edwindertien/picotonewheel/docs/07_pio_allocation.png

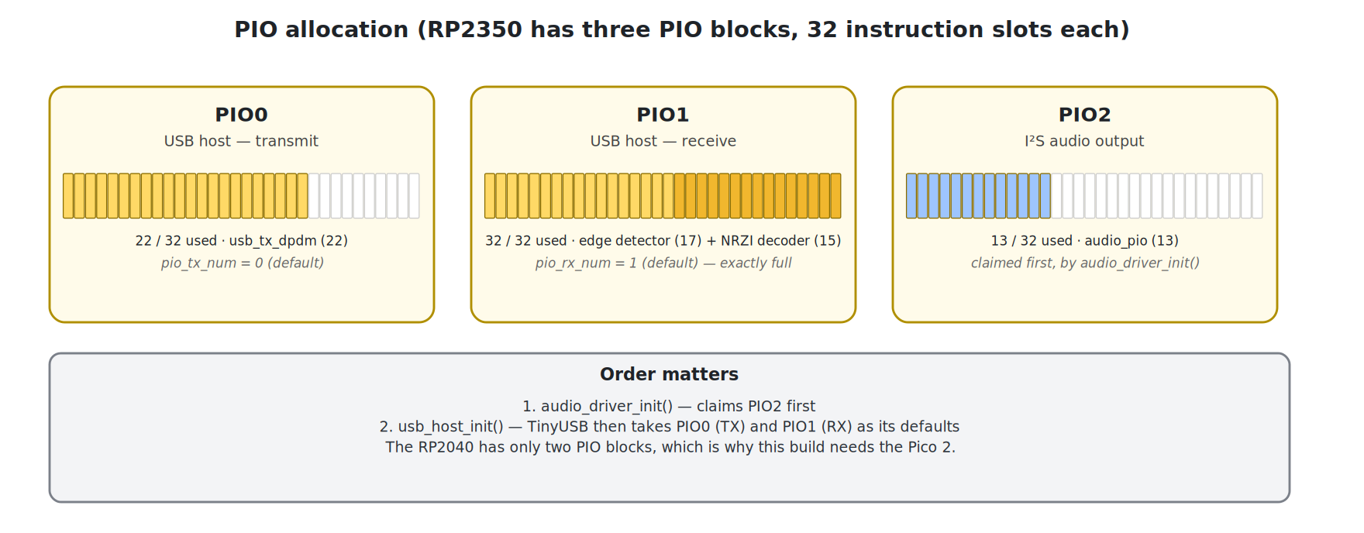
docs/07_pio_allocation.png
