edwindertien/picotonewheel/docs/11_lcd_layout.png

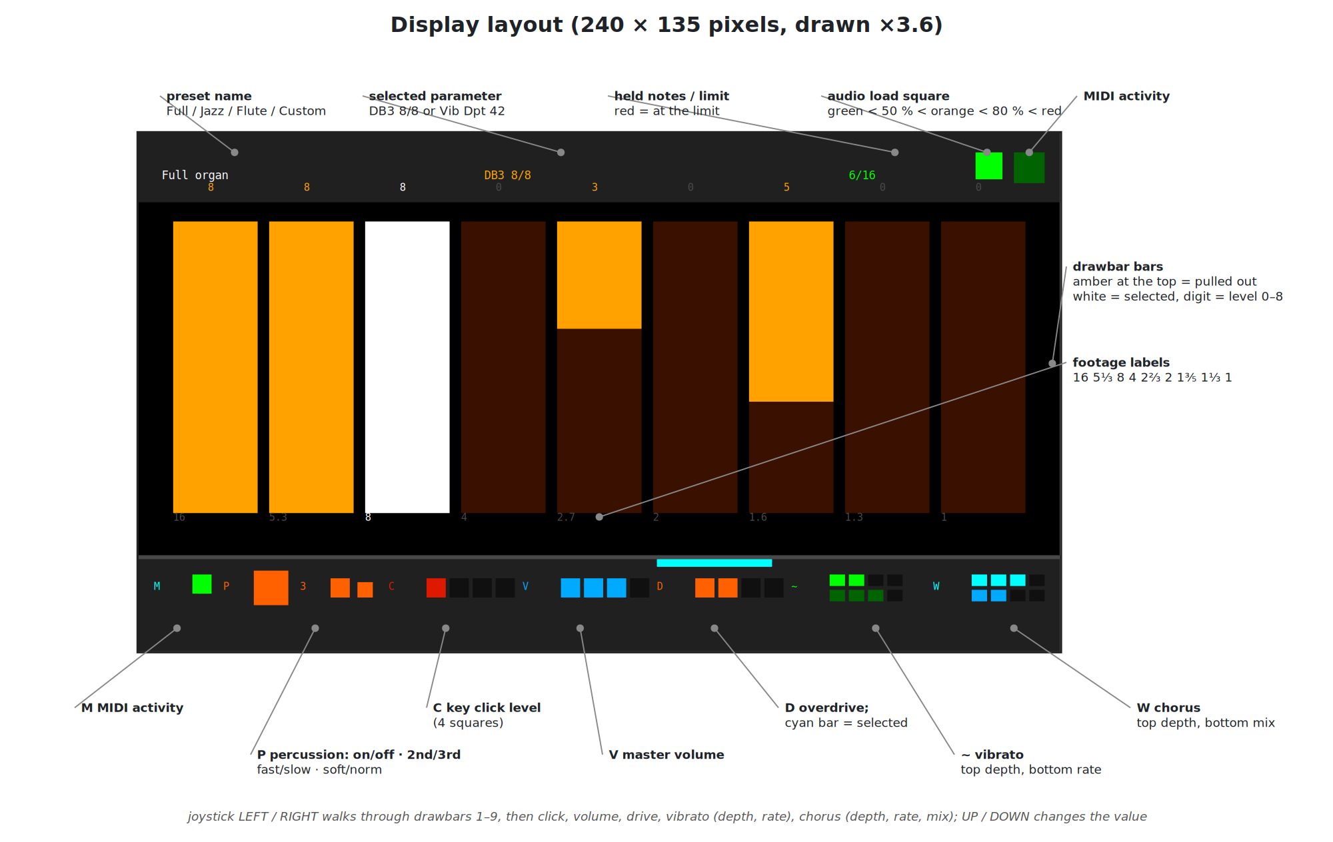
docs/11_lcd_layout.png
