edwindertien/picotonewheel/docs/tonewheel_organ_system.png

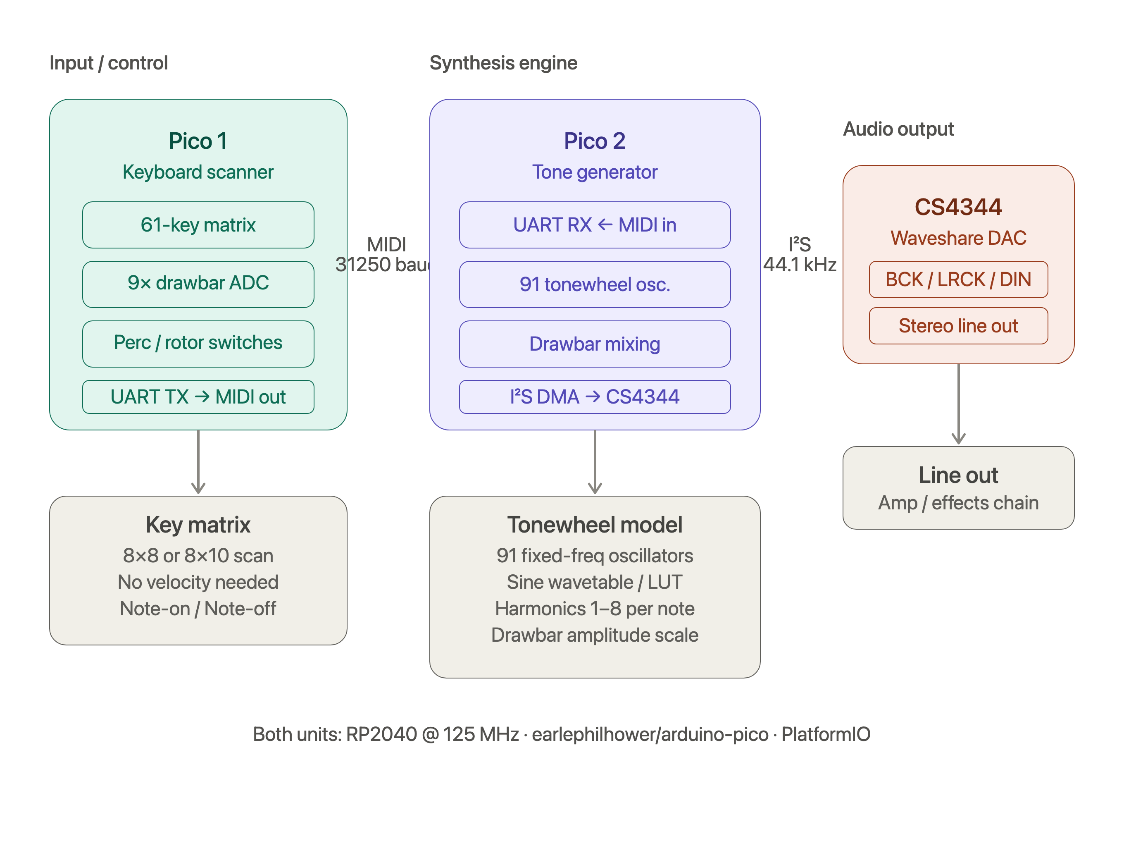
docs/tonewheel_organ_system.png
