edwindertien/picotonewheel/resources/Pico-Audio - Waveshare Wiki_files/300px-Pico-Audio-1.jpg

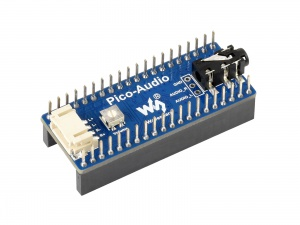
resources/Pico-Audio - Waveshare Wiki_files/300px-Pico-Audio-1.jpg
