edwindertien/picotonewheel/resources/Pico-Audio - Waveshare Wiki_files/300px-Pico-vscode-3.png

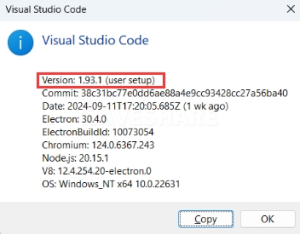
resources/Pico-Audio - Waveshare Wiki_files/300px-Pico-vscode-3.png
