edwindertien/picotonewheel/resources/Pico-Audio - Waveshare Wiki_files/700px-Pico-Audio-details-inte02r.jpg

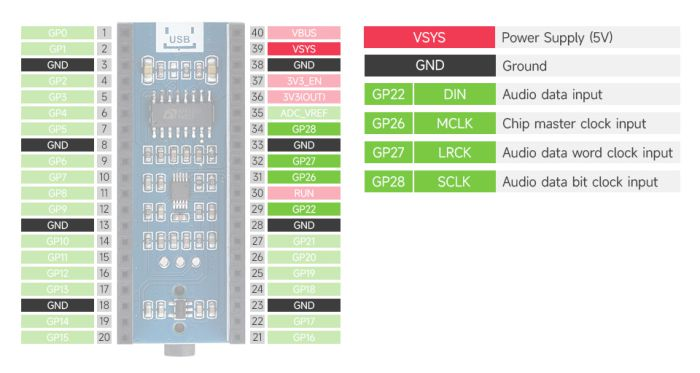
resources/Pico-Audio - Waveshare Wiki_files/700px-Pico-Audio-details-inte02r.jpg
