edwindertien/picotonewheel/resources/Pico-Audio - Waveshare Wiki_files/700px-Pico-R3-Tonny1.png

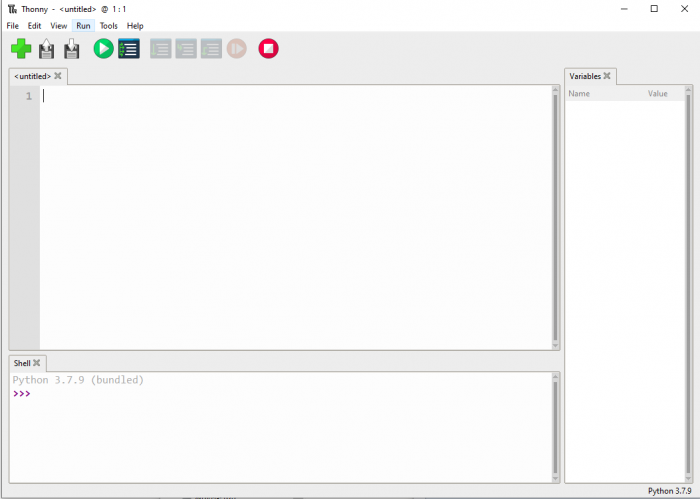
resources/Pico-Audio - Waveshare Wiki_files/700px-Pico-R3-Tonny1.png
