edwindertien/picotonewheel/resources/Pico-Audio - Waveshare Wiki_files/700px-Raspberry-Pi-Pico-Basic-Kit-M-2.png

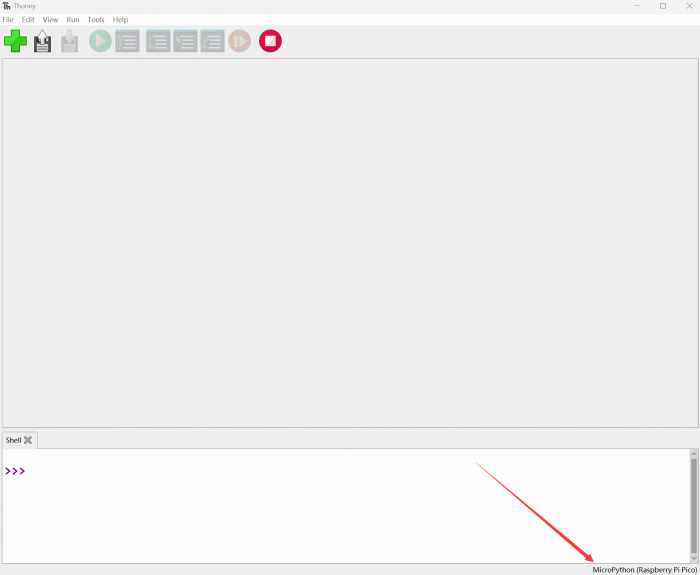
resources/Pico-Audio - Waveshare Wiki_files/700px-Raspberry-Pi-Pico-Basic-Kit-M-2.png
