edwindertien/picotonewheel/resources/Pico-Audio - Waveshare Wiki_files/900px-I2S通信协议1.png

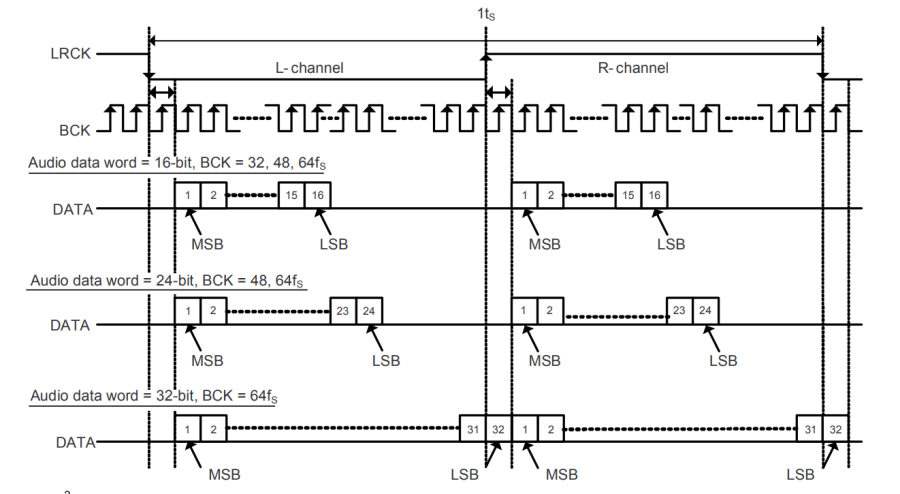
resources/Pico-Audio - Waveshare Wiki_files/900px-I2S通信协议1.png
