edwindertien/picotonewheel/resources/Pico-Audio - Waveshare Wiki_files/2024-09-10_140420.png

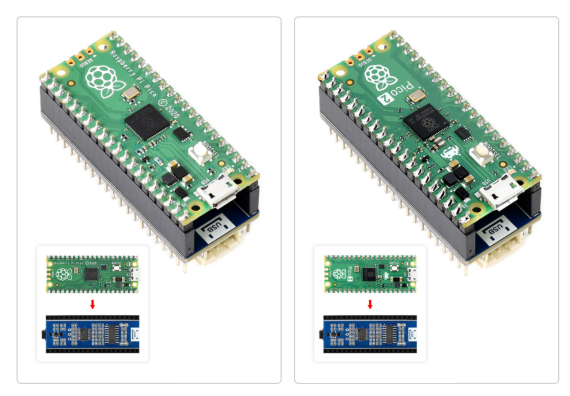
resources/Pico-Audio - Waveshare Wiki_files/2024-09-10_140420.png
