edwindertien/picotonewheel/resources/Pico-Audio - Waveshare Wiki_files/%E9%A6%96%E9%80%89%E9%A1%B9-%E7%AE%80%E4%BD%93%E4%B8%AD%E6%9.jpg

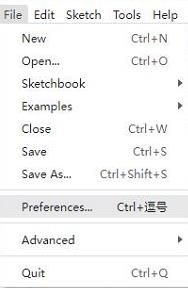
resources/Pico-Audio - Waveshare Wiki_files/%E9%A6%96%E9%80%89%E9%A1%B9-%E7%AE%80%E4%BD%93%E4%B8%AD%E6%9.jpg
