edwindertien/picotonewheel/resources/Pico-Audio - Waveshare Wiki_files/IDE安装水印-1.gif

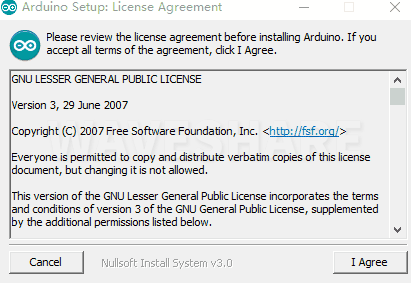
resources/Pico-Audio - Waveshare Wiki_files/IDE安装水印-1.gif
