edwindertien/picotonewheel/resources/Pico-Audio - Waveshare Wiki_files/Pico_Get_Start02.png

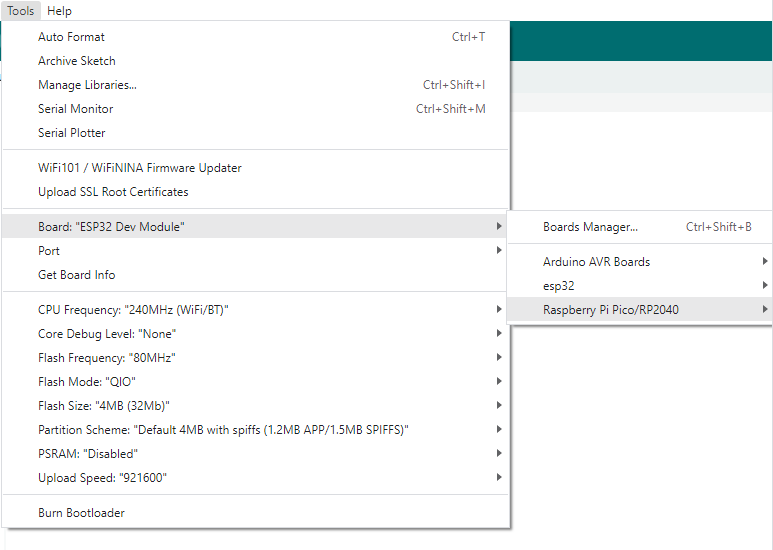
resources/Pico-Audio - Waveshare Wiki_files/Pico_Get_Start02.png
