edwindertien/picotonewheel/resources/Pico-Audio - Waveshare Wiki_files/Raspberry-Pi-Pico2-Python.png

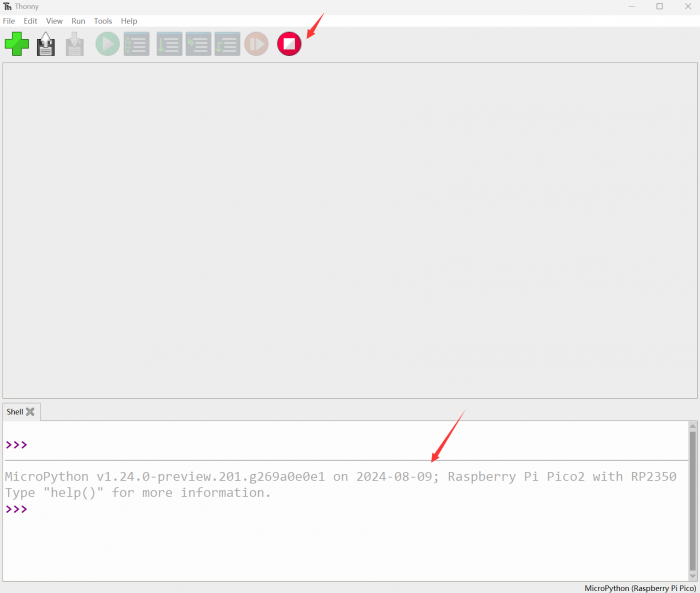
resources/Pico-Audio - Waveshare Wiki_files/Raspberry-Pi-Pico2-Python.png
