edwindertien/picotonewheel/resources/Pico-Audio - Waveshare Wiki_files/仅下载不捐赠.png

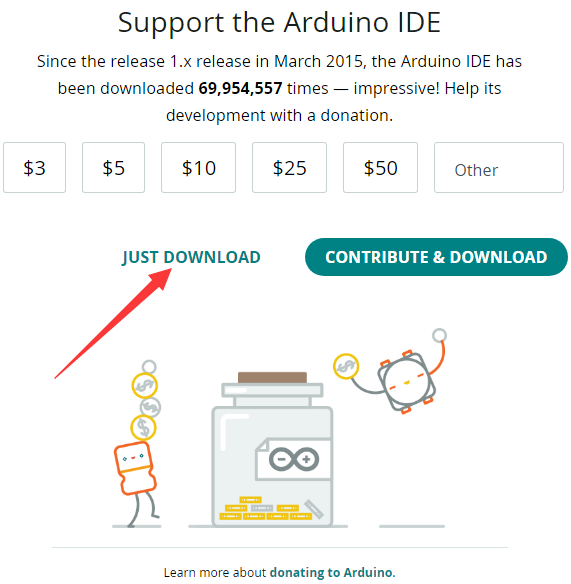
resources/Pico-Audio - Waveshare Wiki_files/仅下载不捐赠.png
