edwindertien/picotonewheel/docs/06_wiring.png

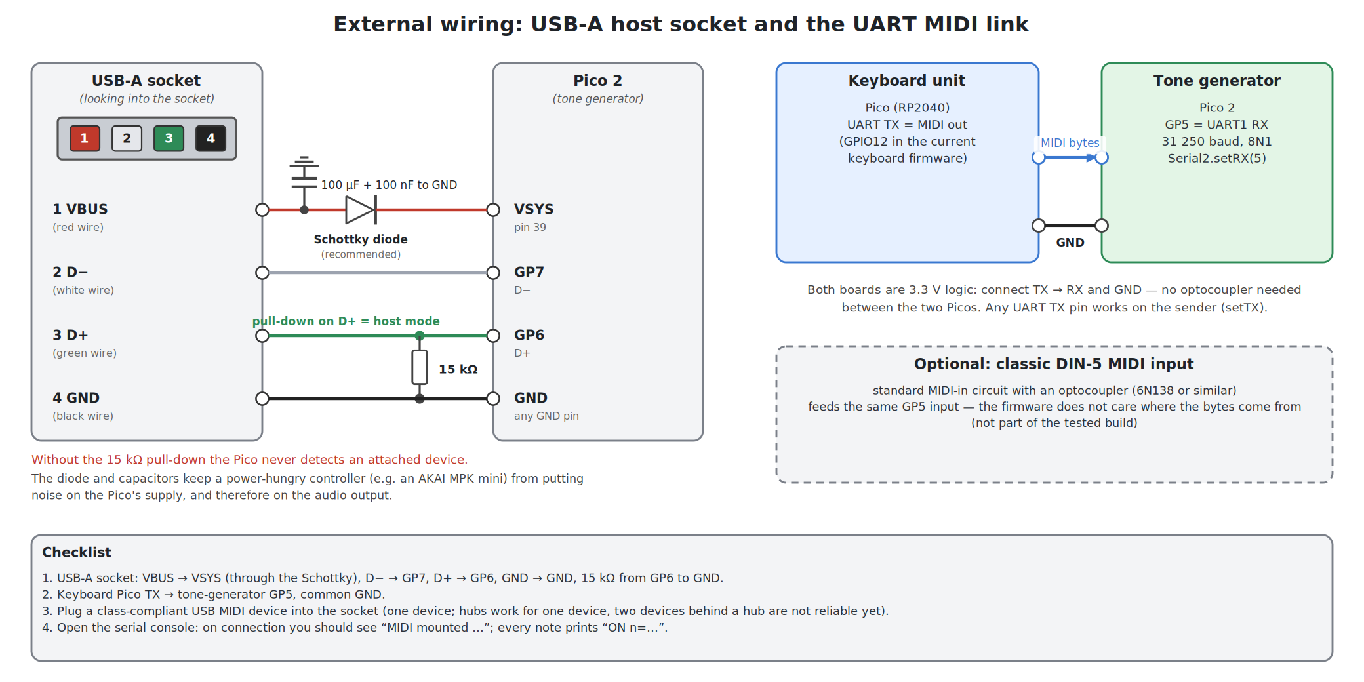
docs/06_wiring.png
