edwindertien/picotonewheel/resources/Pico-Audio - Waveshare Wiki_files/RoArm-M1_Tutorial_II05.jpg

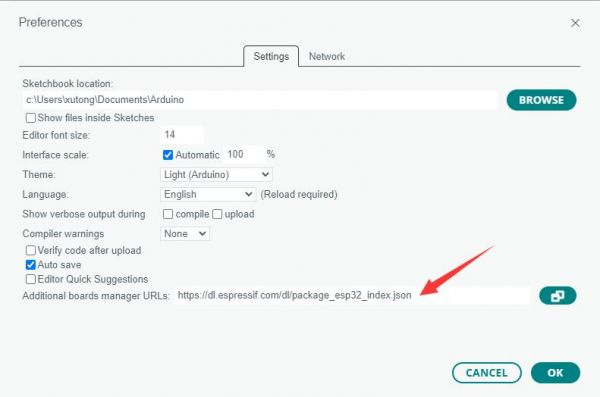
resources/Pico-Audio - Waveshare Wiki_files/RoArm-M1_Tutorial_II05.jpg
